trembl/Uchu-Mini-X/Board/SVG-PCB/No Case/uchu-no-case_interior.png

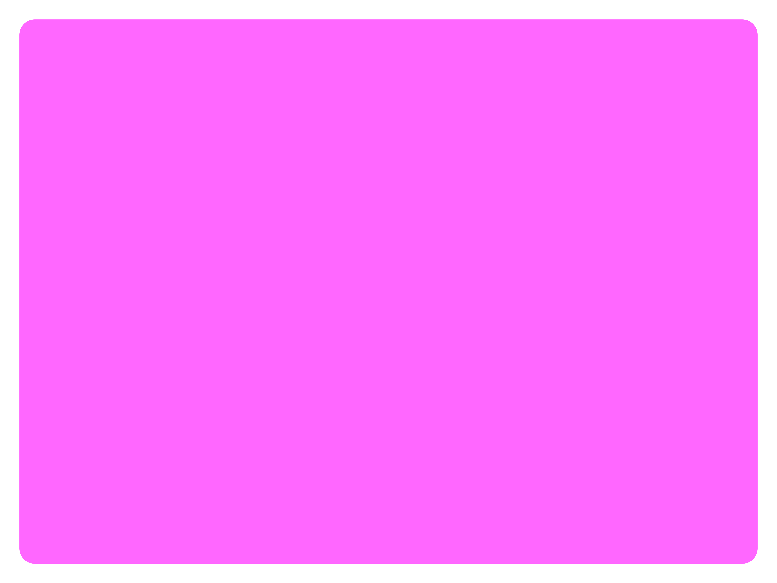
Board/SVG-PCB/No Case/uchu-no-case_interior.png
