trembl/Uchu-Mini-X/Board/SVG-PCB/No Case/uchu-no-case_traces.png

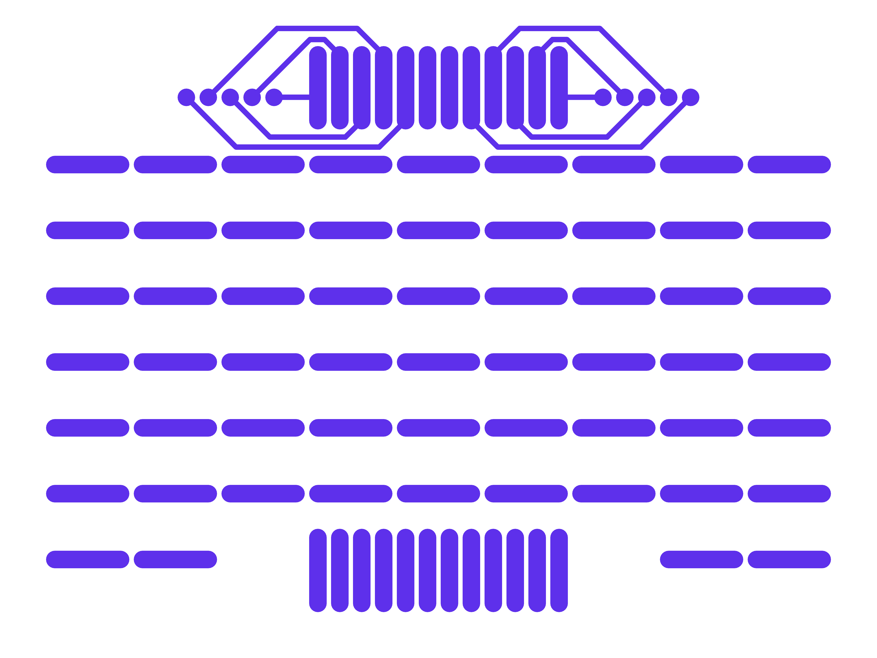
Board/SVG-PCB/No Case/uchu-no-case_traces.png
